BiswasMosam/Desktop-pet/docs/og.png

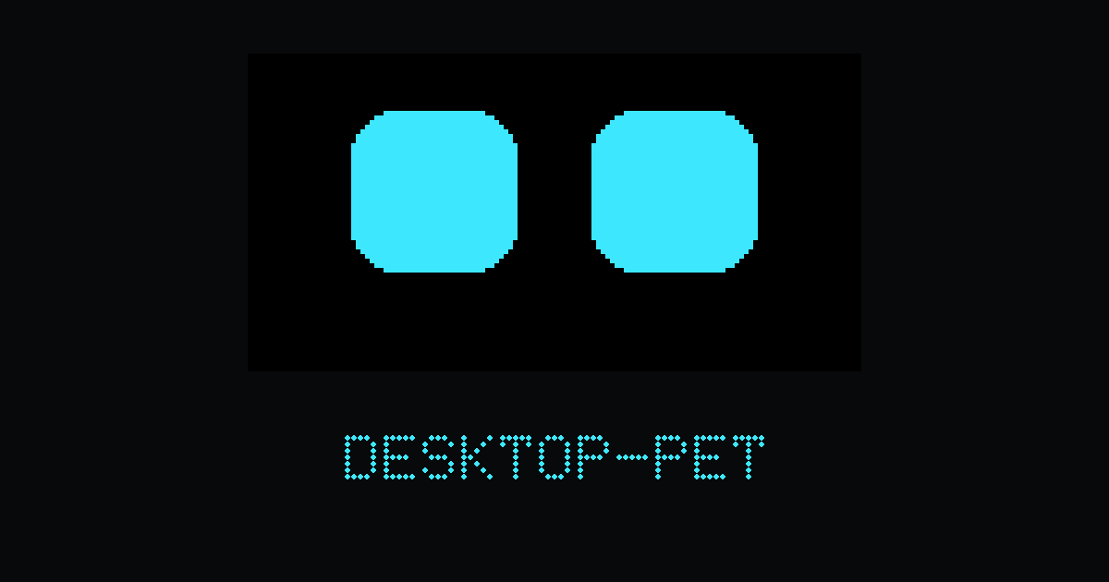
docs/og.png
