BiswasMosam/Desktop-pet/docs/shots/bars.gif

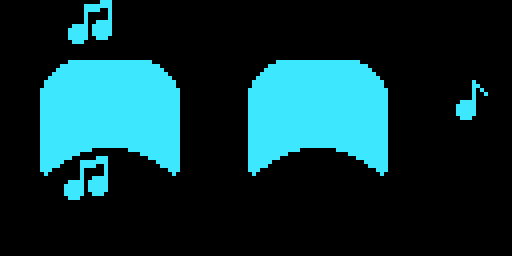
docs/shots/bars.gif
