BiswasMosam/Desktop-pet/docs/shots/card_long.gif

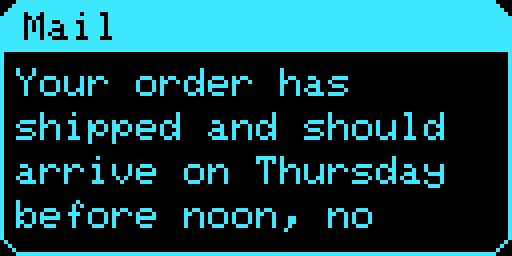
docs/shots/card_long.gif
