BiswasMosam/Desktop-pet/docs/shots/card_open.gif

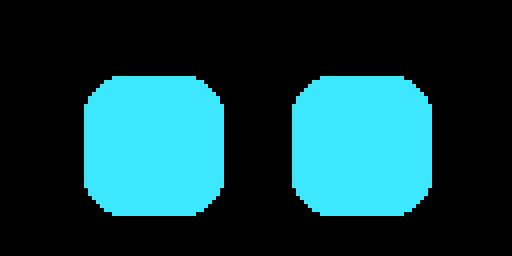
docs/shots/card_open.gif
