BiswasMosam/Desktop-pet/docs/shots/code_music.gif

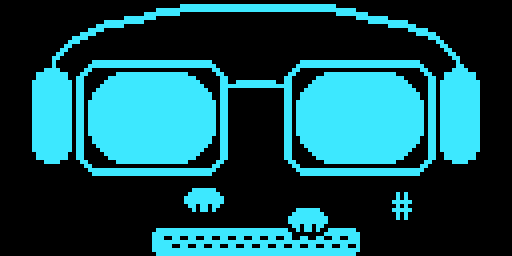
docs/shots/code_music.gif
