BiswasMosam/Desktop-pet/docs/shots/em_love.gif

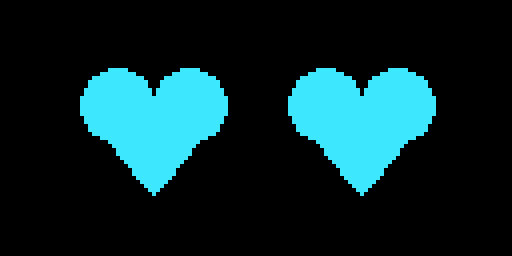
docs/shots/em_love.gif
