BiswasMosam/Desktop-pet/docs/shots/headphones.gif

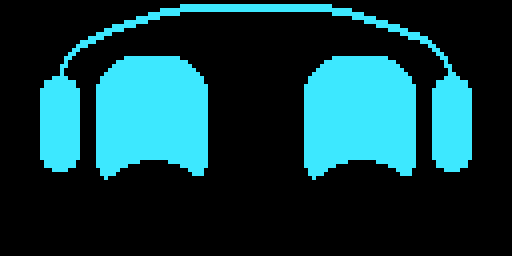
docs/shots/headphones.gif
