BiswasMosam/Desktop-pet/docs/shots/jump.gif

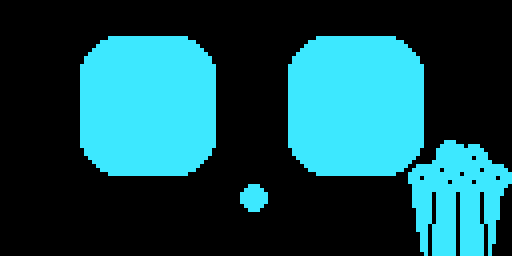
docs/shots/jump.gif
