BiswasMosam/Desktop-pet/docs/shots/listening.gif

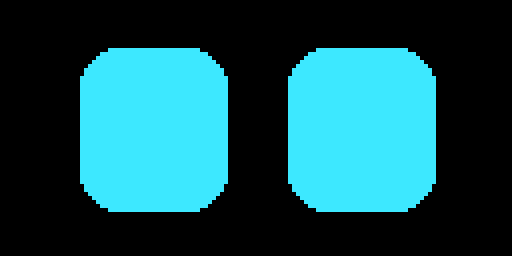
docs/shots/listening.gif
