BiswasMosam/Desktop-pet/docs/shots/selfie.gif

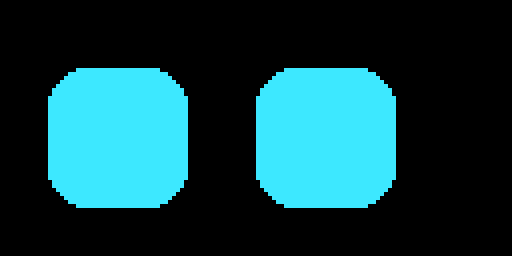
docs/shots/selfie.gif
