BiswasMosam/Desktop-pet/docs/shots/sleepy.gif

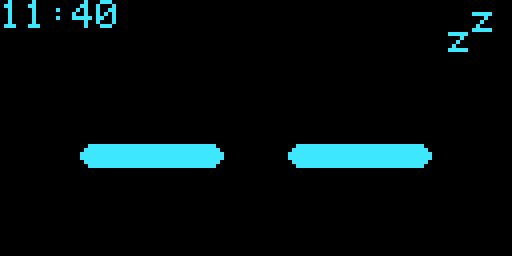
docs/shots/sleepy.gif
