BiswasMosam/Desktop-pet/docs/shots/speaking.gif

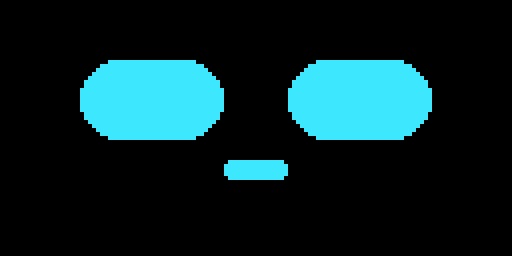
docs/shots/speaking.gif
