BiswasMosam/Desktop-pet/docs/shots/timer.gif

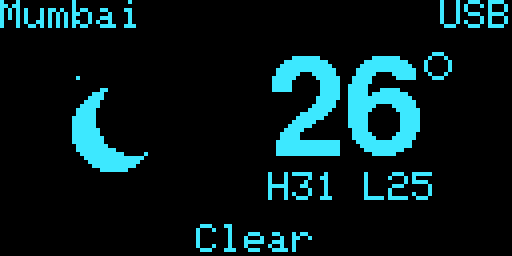
docs/shots/timer.gif
