BiswasMosam/Desktop-pet/docs/shots/timesup.gif

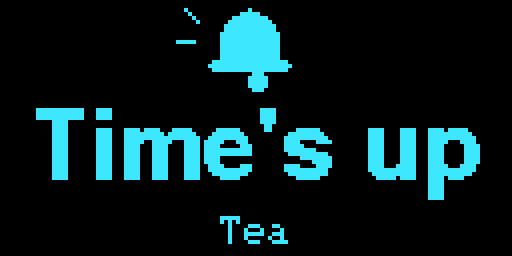
docs/shots/timesup.gif
