BiswasMosam/Desktop-pet/docs/shots/wx_clear.gif

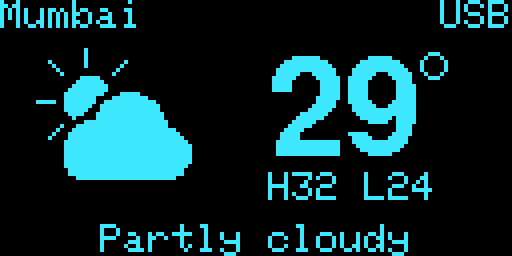
docs/shots/wx_clear.gif
