BiswasMosam/Desktop-pet/docs/shots/wx_night.gif

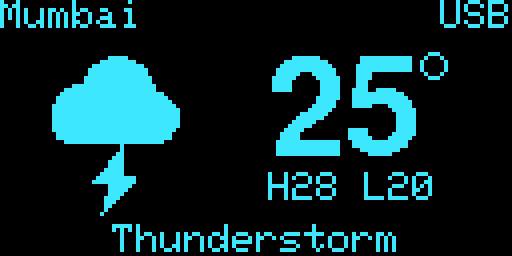
docs/shots/wx_night.gif
