BiswasMosam/Desktop-pet/docs/shots/wx_overcast.gif

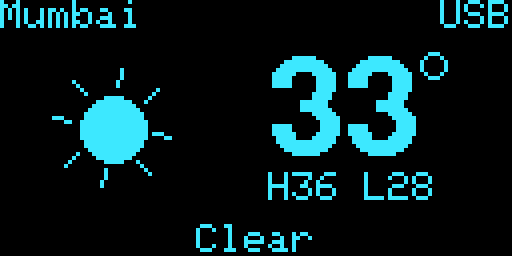
docs/shots/wx_overcast.gif
