BiswasMosam/Desktop-pet/docs/shots/wx_partly.gif

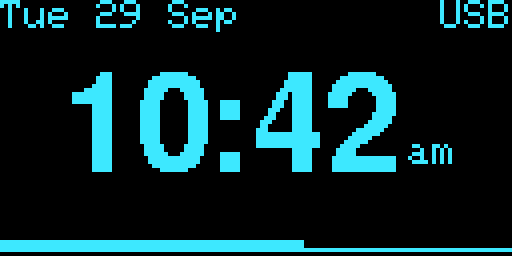
docs/shots/wx_partly.gif
