BiswasMosam/Desktop-pet/docs/shots/wx_snow.gif

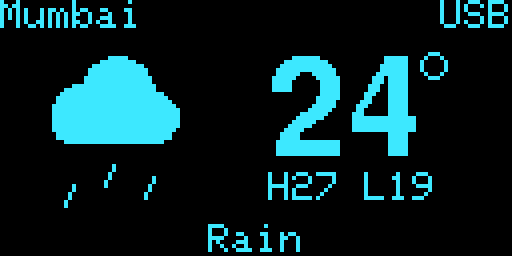
docs/shots/wx_snow.gif
