BiswasMosam/Desktop-pet/docs/shots/wx_storm.gif

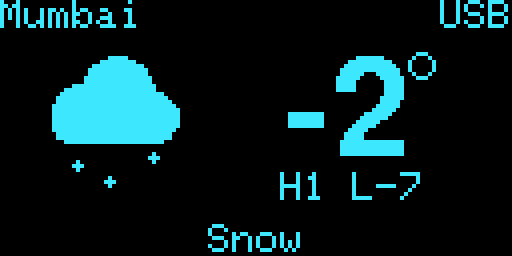
docs/shots/wx_storm.gif
